poetaster/rampart/firmware/DUAL_LFO/DUAL_LFO.ino

///////////////////////////////////////////////////////////////
//
//  Dual LFO
//
//  For each LFO:
//
//  A momentary switch increments through different wave tables
//  One potentiometer to control LFO frequency
//  One potentiometer to control LFO depth
//  A digital input is used to re-trigger/sync the LFO
//
//  The LFOs output to pins 11 (LFO1) and 3 (LFO2). Since the output is PWM, it's
//  important to add low-pass filters to these pins to smooth out the resulting waveform
//
//  See accompanying Fritzing documents for circuit information.


//  The MIT License (MIT)
//
//  Copyright (c) 2013-2018 Robert W. Gallup (www.robertgallup.com)
//  Copyright (c) 2025, Mark Washeim <blueprint@poetaster.de> Rampart version, extra waveforms.
//
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

// Macros for clearing and setting bits
#define cbi(sfr, bit) (_SFR_BYTE(sfr) &= ~_BV(bit))
#define sbi(sfr, bit) (_SFR_BYTE(sfr) |= _BV(bit))

// Used in calculating frequency tuning word
// Create constant to to only calculate 2^32 once
const unsigned long long POW2TO32 = pow(2, 32);

// Output Pins (PWM - digital pins)
// WARNING: Don't change these!
const byte LFO1_OUTPUT_PIN = 9; // 11;
const byte LFO2_OUTPUT_PIN = 10; // 3;

// Control Framework
#include "src/CS_Switch.h"
#include "src/CS_Pot.h"

// wavetables and points in
#include "tables.h"
//#include "Display.h"

#define NUM_WAVES (sizeof(waveTables) / sizeof(byte *))

// LFO Initial wave table numbers
byte LFO1_WaveTableNum = 0;
byte LFO2_WaveTableNum = 0;

#include "Settings.h"

// Calculate LFO frequency ranges
const double LFO1_FREQ_RANGE =    LFO1_FREQ_MAX - LFO1_FREQ_MIN;
const double LFO2_FREQ_RANGE =    LFO2_FREQ_MAX - LFO2_FREQ_MIN;

// Interrupt frequency (16,000,000 / 510)
// 510 is divisor rather than 512 since with phase correct PWM
// an interrupt occurs after one up/down count of the register
// See: https://www.arduino.cc/en/Tutorial/SecretsOfArduinoPWM
const double clock = 31372.549;

// LFO 1 controls
CS_Pot       LFO1_FreqKnob (FREQ1_KNOB_PIN, 3);
CS_Pot       LFO1_DepthKnob (DEPTH1_KNOB_PIN, 3);
CS_Switch    LFO1_WaveSwitch(WAVE1_SWITCH_PIN);

// LFO 2 controls
CS_Pot       LFO2_FreqKnob (FREQ2_KNOB_PIN, 3);
CS_Pot       LFO2_DepthKnob (DEPTH2_KNOB_PIN, 3);
CS_Switch    LFO2_WaveSwitch (WAVE2_SWITCH_PIN);

// Generic pin state variable
byte pinState;

// SYNC variables defined for optional SYNC feature, if defined in Settings.h
#if defined(SYNC)
byte lastSYNC1;
#if !defined(SYNC_COMMON)
byte lastSYNC2;
#endif
#endif

// Interrupt variables are volatile
volatile byte tickCounter;               // Counts interrupt "ticks". Reset every 125
volatile byte fourMilliCounter;          // Counter incremented every 4ms

volatile unsigned long accumulatorA;     // Accumulator LFO1
volatile unsigned long LFO1_TuningWord;  // DDS tuning
volatile unsigned long LFO1_Depth;       // CV depth

volatile unsigned long accumulatorB;     // Accumulator LFO2
volatile unsigned long LFO2_TuningWord;  // DDS tuning
volatile unsigned long LFO2_Depth;       // CV depth

volatile byte *LFO1_WaveTable;
volatile byte *LFO2_WaveTable;

void setup()
{

#if defined(SYNC)
  // Initialize SYNC pin(s) for optional SYNC feature in Settings.h
  pinMode(SYNC1_PIN, INPUT);
  lastSYNC1 = (HIGH == SYNC1_TRIGGER) ? LOW : HIGH;
#if !defined(SYNC_COMMON)
  pinMode(SYNC2_PIN, INPUT);
  lastSYNC2 = (HIGH == SYNC2_TRIGGER) ? LOW : HIGH;
#endif
#endif


  // Initialize PWM Pins
  pinMode(LFO1_OUTPUT_PIN, OUTPUT);     // pin11= PWM:A
  pinMode(LFO2_OUTPUT_PIN, OUTPUT);     // pin 3= PWM:B

  // Initialize knobs
  LFO1_FreqKnob.begin();
  LFO1_DepthKnob.begin();
  LFO2_FreqKnob.begin();
  LFO2_DepthKnob.begin();


  // Initialize wave tables
  LFO1_WaveTable = (byte*)waveTables[0];
  LFO2_WaveTable = (byte*)waveTables[0];

  // Initialize wave switch states
  while (LFO1_WaveSwitch.stateDebounced() == 0);
  while (LFO2_WaveSwitch.stateDebounced() == 0);

  // Initialize timer
  Setup_timer1();

}


void loop()
{

  // SYNC code included if SYNC option defined in Settings.h
#if defined(SYNC)

  // SYNC 1 + SYNC_COMMON
  pinState = digitalRead(SYNC1_PIN);
  if (pinState != lastSYNC1) {
    lastSYNC1 = pinState;
    if (pinState == SYNC1_TRIGGER) {
      accumulatorA = 0;
#if defined(SYNC_COMMON)
      accumulatorB = 0;
#endif
    }
  }

  // Separate SYNC inputs processed if SYNC1 and SYNC2 pins are different
#if !defined(SYNC_COMMON)
  // SYNC 2 (SYNC pins are separate)
  pinState = digitalRead(SYNC2_PIN);
  if (pinState != lastSYNC2) {
    lastSYNC2 = pinState;
    if (pinState == SYNC2_TRIGGER) accumulatorB = 0;
  }
#endif

#endif

  // Check controls every 1/10 second
  if (fourMilliCounter > 25) {
    fourMilliCounter = 0;

    // If DISPLAY defined in Settings.h
#if defined(DISPLAY)
    
#endif

    // LFO 1 wave table switch
    pinState = LFO1_WaveSwitch.stateDebounced();
    if (LFO1_WaveSwitch.changed()) {
      if (pinState == 1) {
        LFO1_WaveTableNum = (LFO1_WaveTableNum + 1) % NUM_WAVES;
        LFO1_WaveTable = (byte*)waveTables[LFO1_WaveTableNum];
      }
    }

    // LFO 2 wave table switch
    pinState = LFO2_WaveSwitch.stateDebounced();
    if (LFO2_WaveSwitch.changed()) {
      if (pinState == 1) {
        LFO2_WaveTableNum = (LFO2_WaveTableNum + 1) % NUM_WAVES;
        LFO2_WaveTable = (byte*)waveTables[LFO2_WaveTableNum];
      }
    }

    // LFO 1 frequency/depth controls
    LFO1_TuningWord = POW2TO32 * (((((double)LFO1_FreqKnob.value() * LFO1_FREQ_RANGE) / 1024L) + LFO1_FREQ_MIN) / clock);
    LFO1_Depth  = LFO1_DepthKnob.value();

    // LFO 2 frequency/depth controls
    LFO2_TuningWord = POW2TO32 * (((((double)LFO2_FreqKnob.value() * LFO2_FREQ_RANGE) / 1024L) + LFO2_FREQ_MIN) / clock);
    LFO2_Depth  = LFO1_DepthKnob.value() + 25; // we are missing a knob, so depth is controlled by one
  }

}

//******************************************************************
// timer1 setup, pins 9/10
//
void Setup_timer1() {

  // Prescaler 1
  sbi (TCCR1B, CS20);
  cbi (TCCR1B, CS21);
  cbi (TCCR1B, CS22);

  // Non-inverted PWM
  cbi (TCCR1A, COM2A0);
  sbi (TCCR1A, COM2A1);
  cbi (TCCR1A, COM2B0);
  sbi (TCCR1A, COM2B1);

  // Phase Correct PWM
  sbi (TCCR1A, WGM20);
  cbi (TCCR1A, WGM21);
  cbi (TCCR1B, WGM22);

  // Enable interrupt
  sbi (TIMSK1, TOIE1);

}

//******************************************************************
// timer2 setup pin 11/3 timer 2
//
void Setup_timer2() {

  // Prescaler 1
  sbi (TCCR2B, CS20);
  cbi (TCCR2B, CS21);
  cbi (TCCR2B, CS22);

  // Non-inverted PWM
  cbi (TCCR2A, COM2A0);
  sbi (TCCR2A, COM2A1);
  cbi (TCCR2A, COM2B0);
  sbi (TCCR2A, COM2B1);

  // Phase Correct PWM
  sbi (TCCR2A, WGM20);
  cbi (TCCR2A, WGM21);
  cbi (TCCR2B, WGM22);

  // Enable interrupt
  sbi (TIMSK2, TOIE2);

}

////////////////////////////////////////////////////////////////
//
// Timer1 Interrupt Service
// Frequency = 16,000,000 / 510 = 31372.5
//
ISR(TIMER1_OVF_vect) {

  byte offset;

  // Count every four milliseconds
  if (tickCounter++ == 125) {
    fourMilliCounter++;
    tickCounter = 0;
  }

  // Sample wave table for LFO1
  accumulatorA  += LFO1_TuningWord;
  offset         = accumulatorA >> 24; // high order byte
  OCR1A          = (pgm_read_byte_near(LFO1_WaveTable + offset) * LFO1_Depth) / 1024L;

  // Sample wave table for LFO2
  accumulatorB  += LFO2_TuningWord;
  offset         = accumulatorB >> 24; // high order byte
  OCR1B          = (pgm_read_byte_near(LFO2_WaveTable + offset) * LFO2_Depth) / 1024L;

}


////////////////////////////////////////////////////////////////
//
// Timer2 Interrupt Service
// Frequency = 16,000,000 / 510 = 31372.5
//
/*
  ISR(TIMER2_OVF_vect) {

  byte offset;

  // Count every four milliseconds
  if (tickCounter++ == 125) {
    fourMilliCounter++;
    tickCounter = 0;
  }

  // Sample wave table for LFO1
  accumulatorA  += LFO1_TuningWord;
  offset         = accumulatorA >> 24; // high order byte
  OCR2A          = (pgm_read_byte_near(LFO1_WaveTable + offset) * LFO1_Depth) / 1024L;

  // Sample wave table for LFO2
  accumulatorB  += LFO2_TuningWord;
  offset         = accumulatorB >> 24; // high order byte
  OCR2B          = (pgm_read_byte_near(LFO2_WaveTable + offset) * LFO2_Depth) / 1024L;

  }
*/
