poetaster/rampart/firmware/rampartGlitchArp/rampartGlitchArp.ino

/*********************************************************************
                     Arpeggiating Glitch Synth
                Mozzi Mod By Turbogoblin/Nugetteero.
          Code G-Rated and Washed by STAR*TRASH ELECTRONICS
 *********************************************************************

   INPUTS:
   modified by blueprint@poetaster.de from the original:
   https://github.com/wadecore/arpeggiatingGlitchSynth
   to work with rampartv3:
   https://github.com/poetaster/rampart

 *********************************************************************/
#include <Mozzi.h>
#include <WavePacket.h>
#include <RollingAverage.h>
#include <AutoMap.h>

const int SENSOR_PIN   = 4; // Pin 4 used for floating value
const int KNOB_PIN     = 0; // Analog input pin 0
const int KNOB_PIN_1   = 1; // Analog input pin 1
const int KNOB_PIN_2   = 2; // Analog input pin 2
const int LDR1_PIN     = 3; // Analog input for fm_intensity to pin 1
const int BUTTON_PIN   = 2;// Digital input pin 2
const int BUTTON_PIN_1 = 4; // Digital input pin 3
const int BUTTON_PIN_2 = 3; // Digital input pin 4
const int BUTTON_PIN_3 = 8; // Digital input pin 8
const int LED_PIN      = 6;// Digital output pin 6  Red LED
const int LED_PIN_1    = 13; // Digital output pin 13 Green LED

int brightness = 0;    // how bright the LED is
int fadeAmount = 5;
int bandwidthMod = 0;
int centre_freq = 52;

//A mess of variables with silly names but perfectly reasonable functions
int heck    = 3;
int dang    = 0;
int alright = 1;
int swotch  = 1;
int cons    = 4;
int button1 = 0;
int button2 = 0;
int button3 = 0;
int button4 = 0;
int con     = 4;
int fun     = 1;
int gosh    = 100;

// min and max values of synth parameters to map AutoRanged analog inputs to
const int MIN_F = 8;
const int MAX_F = 255;
const int MIN_BW = 8;
const int MAX_BW = 1000;
const int MIN_CF = 8;
const int MAX_CF = 1000;
long randNumber;

// variables for reading the pushbutton status
int buttonState  = 0;
int buttonState1 = 0;
int buttonState2 = 0;
int buttonState3 = 0;

// used to inc/dec the iterations running in the audio loop
int alrightcons = 7;

int adjCon = 20;

// for smoothing the control signals
// use: RollingAverage <number_type, how_many_to_average> myThing
RollingAverage <int, 32> kAverageF;
RollingAverage <int, 32> kAverageBw;
RollingAverage <int, 32> kAverageCf;
AutoMap kMapF(0, 1023, MIN_F, MAX_F);
AutoMap kMapBw(0, 1023, MIN_BW, MAX_BW);
AutoMap kMapCf(0, 1023, MIN_CF, MAX_CF);
WavePacket <DOUBLE> wavey; // DOUBLE selects 2 overlapping streams

void setup()
{
  pinMode(BUTTON_PIN, INPUT);
  pinMode(BUTTON_PIN_1, INPUT);
  pinMode(BUTTON_PIN_2, INPUT);
  pinMode(BUTTON_PIN_3, INPUT);
  pinMode(LED_PIN, OUTPUT);
  pinMode(LED_PIN_1, OUTPUT);

  //Serial.begin(9600); // for Teensy 3.1, beware printout can cause glitches
  Serial.begin(115200);
  // wait before starting Mozzi to receive analog reads, so AutoRange will not get 0
  delay(50);
  startMozzi();
}

void updateControl()
{
  int thirdknob = mozziAnalogRead(KNOB_PIN_2) + 1;
  int reading = mozziAnalogRead(SENSOR_PIN);
  float voltage = reading * 5.0;
  float temperatureC = (voltage - 0.5) * 100 ;

  int knobby = mozziAnalogRead(KNOB_PIN) + 1;
  int knibby = mozziAnalogRead(KNOB_PIN_1) + 1;
  int knab = knibby / 10;


  // input A4.
  if (reading > 100 )  {
    knibby = (knibby + reading) / 2;

  }

  //Serial.println(reading);
  int bandwidth = mozziAnalogRead(LDR1_PIN);
  bandwidthMod = mozziAnalogRead(7); // rampart second input pin

  int fundamental = bandwidth ;
  fundamental = kMapF(fundamental);

  bandwidth = kMapBw(bandwidth);

  centre_freq = kMapCf(knibby);

  updateButtons();

  if (alright < alrightcons)
  {
    brightness = 0;    // how bright the LED is
    fadeAmount = 5;
    //centre_freq = 0;
    bandwidth = 0;
    //digitalWrite(LED_PIN, LOW);
    //analogWrite(LED_PIN_1, bandwidth);
  }

  if (alright < con)
  {
    brightness = brightness + fadeAmount;
    // reverse the direction of the fading at the ends of the fade:
    if (brightness == 0 || brightness == 100)
    {
      fadeAmount = -fadeAmount * 4;
    }
  }

  // modulating within the audio loop

  alright = alright + 1;
  con = (thirdknob / 20) + 2; // hmmm, this and cons are tied and change over 16 instead of the initial 8

  // if alright is greater, slower, lesser, faster since the number of iterations on audioupdate
  if (alrightcons > 15) {
    alrightcons = 4;
  }

  if (alright > alrightcons)
  {
    alright = 0;
    swotch = swotch + 10;
  }

  fundamental = fundamental / 4;
  brightness = brightness + con;
  

  if (swotch > 9 && swotch < 20)
  {
    fundamental = fundamental + button1;
    centre_freq = centre_freq - con;
    //digitalWrite(LED_PIN, HIGH);
    digitalWrite(LED_PIN_1, HIGH);

  }

  if (swotch > 19 && swotch < 30)
  {
    fundamental = fundamental + button2;
    brightness = brightness - con;
    centre_freq = centre_freq + con;
    digitalWrite(LED_PIN_1, LOW);
  }

  if (swotch > 29 && swotch < 40)
  {
    fundamental = fundamental + button3;
    brightness = brightness + con;
    centre_freq = centre_freq - con;
    //digitalWrite(LED_PIN, HIGH);
    //analogWrite(LED_PIN_1, fundamental);
    digitalWrite(LED_PIN_1, LOW);
  }

  if (swotch > 39)
  {
    swotch = 0;
    brightness = brightness - con;
    centre_freq = centre_freq + con;
    digitalWrite(LED_PIN_1, HIGH);
  }



  // if we have a modulating signal, use it to modify bandwidth
  if ( bandwidthMod > 50 ) {
    bandwidth = (bandwidth + bandwidthMod) / 2  ;
    //Serial.println(bandwidthMod);
  } else {
    bandwidth = (brightness * 14) + (knobby / 2);
  }
  //Serial.println(bandwidth);

  cons = (con / 10) + 2;
  //cons = map(thirdknob, 0,1023, alrightcons, con);
  Serial.println(centre_freq);
  Serial.println(knibby);
  //Serial.println(cons);
  //Serial.println(con);

  //bandwidth = (brightness * 14) + (knobby / 2);
  centre_freq = (brightness + centre_freq); // * 3);
  //centre_freq = (brightness + centre_freq / 2);
  wavey.set(fundamental, bandwidth, centre_freq);
}


/* all button handling within control update */

void updateButtons() {

  buttonState = digitalRead(BUTTON_PIN);
  buttonState1 = digitalRead(BUTTON_PIN_1);
  buttonState2 = digitalRead(BUTTON_PIN_2);
  buttonState3 = digitalRead(BUTTON_PIN_3);

  // random all this was a button3 only thing.
  if (buttonState2 == HIGH && buttonState1 == HIGH )  {
    Serial.println("random");
    int choose = random(3);
    switch (choose) {
      case 1:
        button1 = random(300 - button1);
        break;
      case 2:
        button3 = random(300 - button3);
        break;
      case 3:
        button2 = random(300 - button2);
        break;

    }
    alrightcons = random(16) + 4;
  }
  if (buttonState == HIGH && buttonState2 == HIGH )  {
    //reset
    Serial.println("reset");
    button1 = 0;
    button2 = 0;
    button3 = 0;
  }
  // works better with random
  if (buttonState == HIGH && buttonState1 == HIGH)  {
    alrightcons = alrightcons + 1;
  }


  if (buttonState1 == HIGH && buttonState2 == LOW && buttonState == LOW)  {
    Serial.println("one");
    button1 = button1 + 1; 
    if (button1 > 250) {
      button1 = 1;
    }
  }

  if (buttonState2 == HIGH && buttonState1 == LOW && buttonState == LOW)
  {
    Serial.println("two");
    button2 = button2 + 1;
    if (button2 > 250) {
      button2 = 1;
    }
  }

  if (buttonState == HIGH && buttonState1 == LOW && buttonState2 == LOW )
  {
    Serial.println("three");
    button3 = button3 + 1;
    if (button3 > 250) {
      button3 = 1;
    }
  }

}


AudioOutput_t  updateAudio() {
  while (alright < cons) {
    return wavey.next() >> 8; // >>8 for AUDIO_MODE STANDARD
  }
}

void loop() {
  audioHook(); // required here
}
