poetaster/rampart/firmware/simple_samples/kick.h

#ifndef kick_H_
#define kick_H_
 
 
#if ARDUINO >= 100
#include "Arduino.h"
#else
#include "WProgram.h"
#endif
#include <avr/pgmspace.h>
 
#define kick_NUM_CELLS 7581
#define kick_SAMPLERATE 16384
 
const int8_t __attribute__((section(".progmem.data"))) kick_DATA [] = {-1, 2, 18, 32, 42, 51, 57, 64, 68,
73, 76, 79, 81, 82, 83, 83, 84, 83, 78, 72, 66, 60, 53, 47, 41, 34, 26, 19, 13,
5, -2, -8, -14, -21, -27, -34, -39, -46, -51, -57, -62, -67, -71, -76, -81, -84,
-87, -91, -94, -97, -100, -102, -104, -106, -106, -108, -107, -106, -105, -103,
-100, -99, -96, -94, -93, -91, -89, -87, -85, -81, -79, -75, -72, -69, -65, -61,
-57, -53, -49, -45, -39, -35, -30, -26, -20, -15, -10, -4, 1, 6, 11, 17, 20, 25,
28, 32, 35, 37, 39, 41, 43, 44, 46, 46, 47, 48, 49, 49, 50, 51, 52, 52, 52, 53,
53, 53, 53, 54, 54, 54, 54, 53, 54, 54, 54, 53, 54, 54, 54, 53, 54, 54, 53, 54,
53, 53, 52, 52, 52, 52, 52, 51, 51, 51, 50, 49, 49, 48, 48, 47, 47, 47, 46, 45,
45, 45, 44, 44, 42, 43, 42, 41, 40, 39, 39, 38, 38, 36, 36, 35, 35, 34, 34, 32,
32, 31, 30, 30, 28, 28, 27, 26, 25, 24, 24, 23, 22, 21, 20, 19, 19, 17, 16, 15,
15, 14, 12, 11, 10, 10, 8, 8, 7, 6, 6, 5, 3, 2, 2, 1, -1, -2, -2, -3, -5, -7,
-7, -8, -9, -11, -11, -12, -14, -15, -16, -17, -19, -20, -21, -23, -24, -25,
-27, -28, -29, -31, -32, -34, -35, -37, -39, -40, -41, -42, -43, -45, -47, -48,
-50, -51, -53, -54, -55, -56, -58, -59, -59, -61, -63, -64, -65, -66, -67, -68,
-69, -71, -71, -72, -72, -73, -75, -76, -77, -77, -77, -77, -77, -79, -78, -80,
-79, -80, -80, -80, -81, -80, -79, -80, -79, -79, -79, -79, -78, -78, -77, -76,
-76, -75, -74, -74, -73, -72, -71, -69, -68, -67, -65, -64, -61, -60, -59, -57,
-55, -53, -51, -50, -47, -46, -43, -41, -39, -37, -35, -34, -32, -29, -27, -25,
-23, -21, -19, -17, -14, -13, -11, -8, -7, -5, -3, -1, 1, 3, 4, 5, 7, 10, 12,
13, 15, 16, 17, 19, 21, 23, 25, 25, 26, 28, 31, 31, 32, 34, 36, 36, 38, 38, 39,
41, 42, 43, 45, 45, 47, 48, 49, 50, 50, 52, 52, 53, 54, 55, 56, 56, 57, 58, 59,
60, 61, 61, 61, 62, 62, 63, 64, 64, 65, 66, 66, 66, 66, 66, 67, 67, 67, 67, 69,
67, 68, 68, 69, 69, 68, 68, 68, 68, 68, 68, 69, 69, 68, 68, 67, 67, 67, 67, 66,
66, 66, 65, 65, 64, 64, 64, 63, 63, 62, 62, 62, 61, 61, 59, 59, 58, 58, 57, 55,
55, 55, 54, 53, 52, 51, 51, 50, 49, 48, 47, 45, 45, 44, 44, 42, 42, 41, 39, 37,
37, 36, 35, 34, 33, 32, 31, 29, 28, 27, 26, 25, 24, 23, 21, 20, 19, 18, 17, 16,
14, 12, 12, 11, 9, 8, 7, 5, 4, 3, 2, 0, 0, -2, -2, -4, -5, -6, -8, -9, -10, -12,
-12, -14, -15, -16, -18, -19, -20, -21, -23, -24, -26, -28, -28, -30, -31, -32,
-34, -35, -37, -38, -40, -41, -43, -44, -46, -47, -48, -49, -51, -52, -52, -55,
-55, -56, -58, -59, -61, -62, -63, -64, -66, -67, -67, -69, -69, -70, -71, -72,
-72, -73, -74, -75, -75, -76, -76, -76, -77, -78, -79, -79, -79, -79, -79, -80,
-79, -80, -80, -79, -79, -78, -78, -78, -78, -77, -77, -77, -77, -75, -75, -74,
-74, -73, -72, -71, -70, -69, -68, -67, -66, -65, -64, -62, -60, -60, -58, -57,
-55, -54, -52, -51, -49, -48, -46, -45, -43, -42, -39, -38, -36, -35, -33, -31,
-29, -27, -26, -24, -22, -21, -18, -17, -15, -13, -12, -10, -8, -7, -5, -3, -2,
0, 1, 3, 4, 6, 8, 9, 11, 11, 14, 14, 15, 17, 19, 20, 21, 23, 23, 25, 26, 27, 29,
30, 32, 33, 33, 34, 35, 36, 38, 39, 40, 40, 41, 43, 43, 44, 44, 46, 47, 48, 48,
49, 50, 50, 52, 52, 52, 53, 54, 54, 55, 56, 56, 57, 56, 57, 58, 59, 59, 60, 60,
60, 59, 60, 61, 61, 61, 61, 62, 62, 62, 61, 62, 62, 62, 63, 62, 62, 62, 62, 62,
62, 62, 63, 62, 61, 62, 61, 61, 61, 61, 61, 61, 60, 60, 60, 59, 58, 59, 58, 58,
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

#endif /* kick_H_ */
