poetaster/rampart/firmware/simple_samples/snare.h

#ifndef snare_H_
#define snare_H_
 
 
#if ARDUINO >= 100
#include "Arduino.h"
#else
#include "WProgram.h"
#endif
#include <avr/pgmspace.h>
 
#define snare_NUM_CELLS 2840
#define snare_SAMPLERATE 16384
 
const int8_t __attribute__((section(".progmem.data"))) snare_DATA [] = {2, -2, 9, 17, -13, -23, -21, -7, 3,
12, 12, 14, 18, 11, 5, 1, 3, 2, -3, -12, -12, -10, -18, -21, -20, -15, -9, -3,
8, 11, 5, -1, -2, 12, 23, 21, 9, -1, -6, -10, -7, 2, 5, 8, 15, 16, 20, 20, 12,
12, 16, 19, 12, 4, -4, -7, -11, -31, -25, -12, -27, -9, -6, -24, -9, -1, -22,
-13, 14, -14, -28, -12, -14, -16, -15, -10, -1, 2, -1, -1, -8, -27, -4, 29, 15,
3, 2, -20, -18, 20, 42, 35, 20, 28, 40, 35, 25, 21, 16, 14, 11, 6, 6, 5, -16,
-26, -15, -3, 1, -19, -14, -10, -19, -5, 3, 9, 16, 18, 19, 23, 20, 8, 2, 2, 4,
-16, -5, 4, -15, -32, -16, -1, -4, 24, 17, 21, 43, 28, 22, 26, -2, -11, 5, 33,
0, -14, 17, -22, -36, -56, -64, -55, -41, -15, -21, -11, -25, -62, -74, -55,
-55, -30, 2, -60, -98, -50, -21, -75, -89, -18, 8, -65, -59, 22, 20, -13, -18,
4, 31, 44, 34, 45, 51, 52, 53, 46, 57, 50, 44, 45, 26, 41, 44, 30, 41, 47, 22,
13, 38, 49, 40, 29, 31, 35, 34, 19, 21, 18, 11, 14, 30, 30, 23, 30, 39, 13, -18,
-5, 30, 2, -42, 13, 22, 17, 9, -10, 16, 18, -4, 15, 30, -58, -108, -64, -5, 1,
-51, 0, 5, -49, -62, -51, -42, -80, -83, -83, -79, -80, -96, -79, -45, -65, -85,
-66, -65, -36, -47, -74, -65, -68, 0, -15, -69, -55, -60, -48, -34, -6, 43, 26,
-38, -17, 23, 54, 9, -14, 44, 58, 48, 52, 38, 45, 72, 63, 56, 46, 57, 64, 58,
51, 62, 62, 51, 44, 46, 59, 46, 36, 53, 58, 47, 31, 43, 51, 37, 26, 22, 25, 34,
44, 24, 25, 24, 9, -21, -3, 28, 0, -23, -15, 14, 44, -8, -62, 5, 24, -25, -63,
-55, -3, 18, -39, -56, -16, 13, -44, -104, -26, 24, -48, -99, -54, -22, -33,
-60, -57, -67, -54, -61, -64, -44, -53, -63, -67, -60, -53, 25, 11, -50, -24, 5,
4, -27, -43, 12, -9, -61, -17, -9, -23, 24, 59, 11, -5, -15, 27, 53, 35, 21, 34,
42, 0, 39, 46, 23, 29, 50, 60, 45, 53, 53, 36, 43, 13, 17, 39, 42, 32, 29, 37,
26, -8, -20, 45, 19, -3, -21, -8, 22, -24, -8, 8, 3, -40, -32, 39, 52, -1, -34,
25, -22, -53, -8, -1, 33, 23, -7, -20, -24, 28, 30, -11, 6, 18, -13, -14, -17,
2, 39, -11, -4, 22, 5, 5, 1, 29, 7, -37, -5, 25, 6, -25, 9, 30, 5, 22, 4, 6, 21,
29, 18, -4, 21, 7, 19, 15, 14, 6, -5, -15, -14, 40, 5, -6, 14, 28, 20, 3, 0, 5,
35, 21, 3, 0, 38, -15, -26, 29, 3, 4, 23, 40, 9, -24, -17, 8, 25, 5, -4, 9, -9,
1, -6, -24, 15, 9, 12, 7, -26, -11, -12, -7, 0, -21, 3, 1, -42, -17, -11, -22,
-22, -4, -8, -39, -27, 9, -21, -62, -37, 0, 4, -24, -23, -21, -10, -6, -23, -36,
-7, -28, -29, -18, -18, 3, 1, 13, 8, -19, -1, 27, 13, 13, -12, 18, 37, 16, 5,
-13, 4, 10, -6, 12, 18, 12, 46, 27, 9, 11, 2, 16, 39, 8, -6, 6, -11, 22, 32, 3,
17, 38, 34, -9, -31, 9, 5, 21, 36, 14, 9, 22, 17, -7, 19, 22, 8, 0, 10, 26, 17,
8, -1, -3, 12, 29, -8, -11, 5, 0, 11, 11, -11, 2, 8, -3, 2, -12, -7, -1, 4, 2,
1, 0, -4, 0, 2, 2, -12, -19, 5, 14, 8, 1, -5, 8, 15, 11, -3, 1, 5, 7, 1, 8, 19,
8, 7, 5, 0, -10, -4, -10, 10, 13, 3, 15, 4, -10, 5, 26, -19, -21, -1, 2, -3, -6,
6, 0, -19, -15, -2, -6, -7, -11, -10, -4, 2, -4, -4, -3, -21, -26, 6, -2, -10,
0, -9, -11, -7, 6, -10, -31, -15, 7, 0, -15, -8, 7, 4, -3, -3, -10, -5, -2, 12,
7, -15, -6, -3, 3, -4, -9, -10, -2, 7, 2, -3, 5, 3, -7, 6, 9, 9, 2, 10, 16, 3,
3, 11, 8, 1, 9, 16, 8, 1, 6, 4, 10, 11, -1, 2, 7, 15, 8, -3, 6, 6, 9, 13, 0, 1,
5, 8, 11, 7, 8, 1, -2, 7, 11, 5, -6, -3, 8, 11, 2, 8, 11, 8, 13, 2, 2, 5, 1, 7,
3, -3, 2, 3, 3, -5, -3, 10, 4, -4, -9, 2, 3, -5, 2, -9, -3, 3, -8, -4, 3, 2, -1,
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

#endif /* snare_H_ */
