poetaster/rampart/firmware/simple_samples/tom.h

#ifndef tom_H_
#define tom_H_
 
 
#if ARDUINO >= 100
#include "Arduino.h"
#else
#include "WProgram.h"
#endif
#include <avr/pgmspace.h>
 
#define tom_NUM_CELLS 2870
#define tom_SAMPLERATE 16384
 
const int8_t __attribute__((section(".progmem.data"))) tom_DATA [] = {0, 0, 0, -1, 0, 0, 1, 4, 5, 5, 4, 3,
2, 3, -83, -128, -99, -72, -50, -46, -38, -40, -36, -29, -22, -19, -10, -4, 3,
9, 16, 23, 29, 32, 39, 43, 46, 49, 52, 54, 55, 56, 56, 57, 55, 53, 51, 44, 44,
44, 42, 38, 36, 36, 35, 34, 33, 32, 32, 30, 30, 29, 29, 28, 28, 28, 27, 27, 26,
25, 26, 25, 25, 25, 24, 24, 24, 24, 19, 15, 16, 17, 18, 18, 20, 14, 7, 8, 11,
13, 12, 5, 2, 5, 8, 6, -2, -2, 1, 3, -4, -6, -3, -1, -7, -10, -5, -6, -13, -12,
-9, -11, -16, -13, -12, -18, -19, -15, -17, -22, -19, -18, -23, -24, -20, -23,
-27, -23, -23, -29, -28, -25, -28, -32, -27, -27, -32, -33, -29, -29, -34, -34,
-29, -31, -36, -35, -32, -30, -36, -38, -35, -31, -31, -38, -37, -35, -32, -30,
-36, -38, -36, -33, -31, -29, -29, -35, -36, -34, -32, -29, -29, -28, -27, -28,
-28, -26, -26, -27, -26, -26, -30, -31, -29, -23, -20, -20, -22, -22, -22, -23,
-22, -21, -22, -21, -21, -20, -15, -11, -13, -14, -13, -7, -7, -7, -2, -2, 0, 4,
4, 8, 9, 12, 13, 16, 18, 20, 23, 25, 27, 28, 31, 31, 33, 34, 35, 37, 37, 39, 39,
41, 39, 39, 41, 39, 42, 41, 37, 41, 42, 39, 35, 36, 40, 40, 37, 34, 32, 31, 30,
33, 37, 36, 34, 31, 30, 29, 29, 28, 27, 27, 26, 26, 25, 26, 25, 24, 24, 20, 15,
16, 16, 18, 19, 20, 19, 19, 20, 14, 8, 9, 11, 13, 15, 12, 7, 3, 6, 8, 10, 5, 0,
1, 3, 4, -1, -4, -2, 1, -2, -7, -6, -3, -5, -10, -9, -7, -9, -13, -11, -10, -13,
-16, -14, -12, -16, -17, -15, -16, -20, -19, -18, -20, -23, -20, -20, -23, -24,
-22, -22, -25, -26, -23, -24, -27, -27, -25, -25, -28, -29, -27, -25, -29, -31,
-29, -26, -27, -32, -32, -30, -27, -25, -30, -33, -32, -29, -26, -25, -28, -33,
-33, -30, -28, -26, -25, -25, -24, -25, -28, -32, -32, -29, -27, -25, -24, -24,
-24, -23, -23, -23, -23, -22, -22, -21, -21, -21, -21, -19, -13, -11, -11, -14,
-15, -15, -15, -10, -7, -7, -8, -5, -2, -2, -2, 1, 2, 5, 7, 8, 10, 11, 14, 15,
17, 18, 20, 22, 24, 26, 27, 28, 29, 30, 30, 31, 33, 34, 34, 34, 35, 34, 34, 36,
35, 34, 36, 35, 33, 34, 36, 35, 34, 31, 29, 31, 34, 35, 33, 31, 29, 27, 27, 26,
26, 25, 25, 25, 24, 24, 23, 23, 22, 23, 23, 22, 21, 21, 20, 21, 20, 20, 19, 15,
11, 11, 13, 13, 15, 15, 15, 10, 6, 6, 7, 9, 10, 8, 3, 3, 4, 5, 5, 0, -1, 0, 2,
0, -3, -4, -3, -2, -5, -7, -5, -5, -7, -9, -8, -8, -10, -12, -11, -11, -13, -14,
-13, -13, -14, -16, -16, -15, -17, -19, -18, -18, -20, -20, -19, -19, -22, -22,
-21, -21, -22, -24, -23, -22, -23, -25, -26, -23, -22, -24, -26, -26, -25, -23,
-24, -26, -26, -27, -24, -23, -24, -27, -28, -27, -24, -23, -22, -21, -24, -28,
-28, -27, -25, -23, -23, -22, -21, -20, -20, -20, -20, -19, -19, -18, -20, -18,
-19, -18, -17, -18, -18, -17, -18, -17, -17, -16, -16, -13, -10, -8, -8, -9,
-10, -9, -4, -4, -3, -2, -1, 0, 3, 4, 5, 7, 9, 10, 11, 13, 14, 15, 16, 18, 20,
21, 22, 23, 24, 26, 27, 26, 28, 29, 30, 30, 30, 31, 31, 31, 31, 31, 30, 30, 31,
31, 31, 28, 29, 30, 32, 31, 29, 27, 26, 24, 24, 24, 24, 27, 28, 29, 28, 26, 24,
24, 23, 22, 22, 22, 21, 22, 20, 16, 13, 13, 13, 14, 16, 16, 17, 16, 16, 16, 14,
11, 8, 7, 9, 9, 10, 10, 7, 5, 4, 5, 5, 6, 4, 2, 1, 2, 2, 1, -1, -2, -1, -1, -3,
-4, -5, -4, -4, -7, -8, -6, -8, -9, -9, -9, -9, -11, -13, -12, -12, -12, -14,
-13, -13, -15, -16, -16, -14, -15, -17, -18, -16, -18, -19, -19, -19, -19, -20,
-20, -20, -19, -19, -21, -22, -22, -21, -20, -22, -23, -23, -21, -21, -20, -22,
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

#endif /* tom_H_ */
