poetaster/rampart/firmware/simple_samples/beats.h

// order of samples: kick, hat, snare, rim, tom
 
#if ARDUINO >= 100
#include "Arduino.h"
#else
#include "WProgram.h"
#endif
#include <avr/pgmspace.h>
#define NUM_BEATS 24

const byte beats[NUM_BEATS][5][4] PROGMEM = {
  { // you can leave your hat on
    {B00000000,B00000000,B00000000,B00000000,},
    {B10101010,B10101010,B10101010,B10101010,},
    {B00000000,B00000000,B00000000,B00000000,},
    {B00000000,B00000000,B00000000,B00000000,},
    {B00000000,B00000000,B00000000,B00000000,},
  },
  { // johnny two hats
    {B00000000,B00000000,B00000000,B00000000,},
    {B11111111,B11111111,B11111111,B11111111,},
    {B00000000,B00000000,B00000000,B00000000,},
    {B00000000,B00000000,B00000000,B00000000,},
    {B00000000,B00000000,B00000000,B00000000,},
  },
  { // drum lesson
    {B10000000,B10000000,B10000000,B10000000,},
    {B10101010,B10101010,B10101010,B10101010,},
    {B00001000,B00001000,B00001000,B00001000,},
    {B00000000,B00000000,B00000000,B00000000,},
    {B00000000,B00000000,B00000000,B00000000,},
  },
  { // half time rock
    {B10000000,B00000000,B10000000,B00000000,},
    {B10101010,B10101010,B10101010,B10101010,},
    {B00000000,B10000000,B00000000,B10000000,},
    {B00000000,B00000000,B00000000,B00000000,},
    {B00000000,B00000000,B00000000,B00000000,},
  },
  { // there there
    {B10000010,B00100000,B10000010,B00100000,},
    {B00000000,B00000000,B00000000,B00000000,},
    {B00001000,B00001000,B00001000,B00001000,},
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
    {B00000000,B10000000,B00001000,B00001000,},
  },
  { // take five
    {B10000000,B00000000,B00001000,B00000000,},
    {B10001010,B10001010,B10001000,B10101000,},
    {B00000010,B00001000,B00100000,B00100000,},
    {B00001000,B00001000,B00000000,B10000000,},
    {B00000000,B00000000,B00000000,B00000000,},
  },
  { // unsquare
    {B10001000,B10000010,B00100010,B00001010,},
    {B00100010,B00101000,B10001000,B10100000,},
    {B00100010,B00101000,B10001000,B10100000,},
    {B00100010,B00101000,B10001000,B10100000,},
    {B00000000,B00000000,B00000000,B00000000,},
  },
  { // nihil (could possibly remove this to save some bytes)
    {B00000000,B00000000,B00000000,B00000000,},
    {B00000000,B00000000,B00000000,B00000000,},
    {B00000000,B00000000,B00000000,B00000000,},
    {B00000000,B00000000,B00000000,B00000000,},
    {B00000000,B00000000,B00000000,B00000000,},
  },
};
