poetaster/rampart/firmware/simple_samples/closedhat.h

#ifndef closedhat_H_
#define closedhat_H_
 
 
#if ARDUINO >= 100
#include "Arduino.h"
#else
#include "WProgram.h"
#endif
#include <avr/pgmspace.h>
 
#define closedhat_NUM_CELLS 1527
#define closedhat_SAMPLERATE 16384
 
const int8_t __attribute__((section(".progmem.data"))) closedhat_DATA [] = {0, 2, -2, 6, -2, -3, 0, -3, -1,
7, -7, 2, 5, -6, -4, 9, -6, 4, -3, -10, 24, -17, 0, 6, -12, 20, -20, 9, 3, -20,
23, -19, 9, -6, 3, 3, -2, 0, -3, 7, -6, 4, 1, -3, 1, 4, -8, 11, -7, -1, 5, -5,
4, -1, -4, 8, -7, 0, 0, 13, -17, 9, -3, -1, 5, -12, 13, -20, 16, -8, -11, 15,
-4, -15, 24, -25, 18, -15, -10, 47, -42, 20, -10, -1, 16, -14, -6, 10, 1, -20,
36, -50, 41, -18, -18, 37, -60, 46, -40, 14, 8, -21, -5, 14, 2, -29, 43, -36,
18, -9, 6, 6, -42, 46, -45, 21, -3, -4, -3, 14, 9, -31, 32, -33, 38, -42, 2, -2,
-34, 37, -29, 13, -11, 21, -16, -2, 32, -49, 28, -19, 13, -22, 25, 6, -30, 25,
-9, -3, -3, 22, -37, 46, -30, 8, 10, -4, -1, -15, 25, -29, 19, -4, 3, 11, -23,
24, -12, -8, 29, -17, -9, 15, 6, -14, 7, 6, -13, 2, 16, -29, 23, -10, -3, 17,
-23, 23, -47, 24, -11, -24, 42, -40, 26, -16, 7, -11, -3, 7, -13, 7, -6, 21,
-25, 18, -2, 11, -26, 30, -1, -24, 26, -11, 9, -31, 15, -11, -24, 36, -42, 30,
-4, -18, 26, -33, 26, -31, 12, 1, -4, -4, 9, 13, -25, 30, -6, -16, 23, -29, 26,
-16, -4, 24, -30, 24, 1, -29, 17, -4, -28, 34, -36, 34, -22, 4, 11, -23, 29,
-29, 4, 17, -15, -5, 16, 9, -16, 7, 12, -14, 11, -14, 25, -26, 5, 11, -30, 36,
-24, -4, 19, -19, 13, -16, 5, 9, -28, 34, -10, -13, 29, -28, 17, -1, -2, 0, -20,
30, -29, 8, 15, -23, 18, -2, 6, -8, -6, 21, -21, 16, 1, 0, -9, -2, 15, -29, 29,
-13, -11, 27, -25, 18, -10, -2, 12, -21, 21, -12, 0, 15, -14, 15, -7, 8, -3,
-13, 27, -32, 20, -4, -5, 13, -14, 13, 11, -23, 20, -10, -7, 17, -31, 26, -20,
15, -10, 10, 4, -15, 16, -17, 21, -19, 10, -1, -15, 29, -31, 18, -6, -4, 16,
-19, 11, -2, -7, 8, 5, -20, 21, -19, 10, 0, -5, 20, -27, 17, -4, -10, 18, -15,
5, 6, 3, -14, 16, -2, -16, 18, -16, 11, -9, 3, 6, -8, 2, 6, -9, 11, -1, -4, 5,
2, 1, -11, 18, -6, -8, 7, 2, -1, -4, 10, -6, -1, 9, -15, 4, 5, -5, -1, 7, -3,
-7, 9, 4, -15, 11, -1, -11, 13, -4, 2, -1, -9, 10, -11, 9, -6, 0, 5, -6, 11,
-15, 17, -14, 1, 6, -4, -7, 4, 6, -16, 18, -6, -9, 13, -7, 5, -5, 7, -4, -5, 9,
-1, -6, 2, 9, -15, 21, -18, 6, 4, -9, 7, 0, -4, -1, 6, -4, 2, 1, -6, 7, -4, -2,
7, -9, 7, -2, 3, -9, 8, -9, 7, -2, -1, 6, -12, 17, -13, 4, 3, -9, 9, -2, -6, 7,
-6, -1, 6, -8, 4, -3, 0, 7, -9, 8, -6, 1, 4, -8, 6, 4, -11, 6, 2, -12, 13, -4,
-9, 14, -13, 5, 4, -9, 14, -13, 9, 2, -11, 13, -10, 1, 7, -7, 5, -6, 6, -1, -5,
7, -6, 1, 0, 6, -7, -4, 12, -13, 7, -2, 3, -6, 3, 3, -13, 17, -11, 1, 6, -3, -3,
5, -4, 3, 1, 0, 1, -9, 12, -9, 1, 6, -11, 11, -7, 5, -4, -2, 10, -16, 13, -7, 2,
-6, 2, 6, -12, 13, -10, 6, 2, -4, -1, -2, 10, -9, 0, 4, -2, -7, 9, -3, -3, 3,
-3, 8, -8, 8, -12, 8, -2, -4, 9, -9, 10, -9, 3, 4, -12, 10, -2, -5, 8, -7, 4, 0,
-3, 4, -8, 9, -4, -3, 5, -2, -1, -3, 7, -6, 1, 1, -4, 7, -7, 3, 0, -6, 8, -9, 6,
-2, -4, 6, -4, 2, 1, -5, 3, 0, -3, 4, -7, 6, -7, 4, -3, 3, -5, -2, 9, -11, 8,
-2, -3, 8, -11, 8, -1, -5, 8, -11, 8, -6, 3, 0, -3, 7, -5, -2, 5, -3, -2, 4, -2,
0, -1, 3, -3, -1, 7, -9, 4, 0, 0, -3, 0, 5, -9, 9, -9, 6, -3, -2, 5, -8, 7, -3,
-4, 7, -5, 2, -2, 0, 3, -7, 7, -6, 0, 4, -5, -3, 6, -4, 0, 1, -1, -1, -2, 7, -7,
4, 1, -1, -2, 1, 6, -9, 8, -5, 1, 1, -2, 3, -6, 4, -2, -3, 4, 0, -3, 3, -1, -1,
-1, 5, -6, 1, 4, -5, 3, 0, -3, 2, -2, 1, -2, -1, 5, -8, 3, 0, -3, 3, -2, -2, 2,
0, 0, 1, -4, 5, -1, -3, 3, -2, -2, 2, 0, 0, -1, 0, 2, -4, 4, -1, -3, 7, -6, 4,
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

#endif /* closedhat_H_ */
